rodan/playa/beaglebone/usermode/vs1063.c

#include <unistd.h>
#include <stdlib.h>
#include <string.h>
#include <sys/stat.h>
#include <fcntl.h>
#include <stdio.h>

#include "config.h"
#include "vs1063.h"
#include "event_gpio.h"
#include "spi.h"

//#include "patches/vs1063a-encpatches.plg"
//#include "patches/vs1063a-encpatchesflac.plg"
//#include "patches/vs1063a-patches-latm.plg"
//#include "patches/vs1063a-patches.plg"
//#include "patches/vs1063a-playflaccrc.plg"
#include "patches/vs1063a-playpatches.plg"

// How many transferred bytes between collecting data.
// A value between 1-8 KiB is typically a good value.
// If REPORT_ON_SCREEN is defined, a report is given on screen each time
// data is collected.
#define REPORT_INTERVAL 8192

uint8_t vs_vol_r, vs_vol_l;
int spidev_fd_xCS, spidev_fd_xDCS;
struct spi_ioc_transfer tr_xCS, tr_xDCS;

uint32_t vs_sm_state;
uint32_t vs_sm_target;
vs_stream_t vs_stream;

//int fd_debug;

void vs_set_state(const uint32_t state)
{
    vs_sm_state = state;
}

void vs_set_target(const uint32_t state)
{
    vs_sm_target = state;
}

void vs_assert_xreset()
{
    gpio_set_value(RST_GPIO, 0);
}

void vs_deassert_xreset()
{
    gpio_set_value(RST_GPIO, 1);
}

uint32_t vs_get_dreq()
{
    uint32_t ret;
    gpio_get_value(DREQ_GPIO, &ret);
    return ret;
}

// read the 16-bit value of a VS10xx register
uint16_t vs_read_register(const uint8_t address, const uint8_t flags)
{
    uint16_t rv = 0;
    uint8_t tx[4] = { VS_READ_COMMAND, address, 0xff, 0xff };
    uint8_t rx[4] = { 0, 0, 0, 0 };

    if (flags == WAIT_FOR_DREQ) {
        vs_wait(VS_DREQ_TMOUT);
    }
    spi_transfer(rx, tx, 4, spidev_fd_xCS, &tr_xCS);
    rv = rx[2] << 8 | rx[3];
    if (flags == WAIT_FOR_DREQ) {
        vs_wait(VS_DREQ_TMOUT);
    }
    return rv;
}

// write VS10xx register
void vs_write_register_hl(const uint8_t address, const uint8_t highbyte, const uint8_t lowbyte,
                          const uint8_t flags)
{
    uint8_t tx[4] = { VS_WRITE_COMMAND, address, highbyte, lowbyte };
    uint8_t rx[4] = { 0, 0, 0, 0 };
    if (flags == WAIT_FOR_DREQ) {
        vs_wait(VS_DREQ_TMOUT);
    }
    spi_transfer(rx, tx, 4, spidev_fd_xCS, &tr_xCS);
    if (flags == WAIT_FOR_DREQ) {
        vs_wait(VS_DREQ_TMOUT);
    }
}

// write VS10xx 16-bit SCI registers
void vs_write_register(const uint8_t address, const uint16_t value, const uint8_t flags)
{
    uint8_t highbyte;
    uint8_t lowbyte;

    highbyte = (value & 0xff00) >> 8;
    lowbyte = value & 0x00ff;
    vs_write_register_hl(address, highbyte, lowbyte, flags);
}

// read data rams
uint16_t vs_read_wramaddr(const uint16_t address)
{
    uint16_t rv = 0;
    vs_write_register(SCI_WRAMADDR, address, WAIT_FOR_DREQ);
    rv = vs_read_register(SCI_WRAM, WAIT_FOR_DREQ);
    return rv;
}

// write to data rams
void vs_write_wramaddr(const uint16_t address, const uint16_t value)
{
    vs_write_register(SCI_WRAMADDR, address, WAIT_FOR_DREQ);
    vs_write_register(SCI_WRAM, value, WAIT_FOR_DREQ);
}

uint8_t vs_xfer_test(uint16_t value1, uint16_t value2)
{
    uint16_t ret_val1, ret_val2;

    vs_write_register(SCI_AICTRL1, value1, WAIT_FOR_DREQ);
    vs_write_register(SCI_AICTRL2, value2, WAIT_FOR_DREQ);

    ret_val1 = vs_read_register(SCI_AICTRL1, WAIT_FOR_DREQ);
    ret_val2 = vs_read_register(SCI_AICTRL2, WAIT_FOR_DREQ);

    if (ret_val1 != value1) {
        printf("%d != %d\n", ret_val1, value1);
        return EXIT_FAILURE;
    }
    if (ret_val2 != value2) {
        printf("%d != %d\n", ret_val2, value2);
        return EXIT_FAILURE;
    }

    vs_write_register(SCI_AICTRL1, 0, WAIT_FOR_DREQ);
    vs_write_register(SCI_AICTRL2, 0, WAIT_FOR_DREQ);

    ret_val1 = vs_read_register(SCI_AICTRL1, WAIT_FOR_DREQ);
    ret_val2 = vs_read_register(SCI_AICTRL2, WAIT_FOR_DREQ);

    if (ret_val1 != 0) {
        return EXIT_FAILURE;
    }
    if (ret_val2 != 0) {
        return EXIT_FAILURE;
    }

    return EXIT_SUCCESS;
}

// wait for VS_DREQ to get HIGH before sending new data to SPI
uint8_t vs_wait(uint16_t timeout)
{
    while (timeout--) {
        if (vs_get_dreq()) {
            return EXIT_SUCCESS;
        }
        usleep(15);
    }
    return EXIT_FAILURE;
}

// DREQ interrupt handler
static void vs1063_handler(unsigned int gpio)
{
    //event_detected(gpio);
    vs_state_machine();
}

void vs_close()
{
    // switch to blocking functions after the IRQ is disabled
    //vs_set_target(VS_SMT_STOP);
    //vs_set_state(VS_SM_IDLE);
    remove_edge_detect(DREQ_GPIO);
    usleep(1000);

    //vs_set_volume(0xfe, 0xfe);
    vs_end_play();

    close(spidev_fd_xCS);
    close(spidev_fd_xDCS);
    gpio_unexport(RST_GPIO);
    gpio_unexport(DREQ_GPIO);
}

void vs_soft_reset(void)
{
    vs_write_register(SCI_MODE, SM_SDINEW | SM_RESET, WAIT_FOR_DREQ);
    usleep(2000);
    vs_write_register(SCI_CLOCKF, 0xb000, WAIT_FOR_DREQ);
    usleep(200);
}

// setup I2S (see page77 of the datasheet of vs1053 )
// also enables blinky lights on the simple dsp evaluation board
void vs_setup_i2s(void)
{
    //set GPIO0 as output
    vs_write_wramaddr(0xc017, 0x00f0);
    //enable I2S (MCLK enabled, 48kHz sample rate)
    vs_write_wramaddr(0xc040, 0x000c);  // I2S_CF_MCLK_ENA | I2S_CF_ENA
}

// set VS10xx volume attenuation    0x00 lound - 0xfe silent
void vs_set_volume(const uint8_t leftchannel, const uint8_t rightchannel)
{
    // volume = dB/0.5
    vs_write_register_hl(SCI_VOL, leftchannel, rightchannel, WAIT_FOR_DREQ);
}

// returns 0 on success
// returns the old codec id on failure
uint16_t vs_end_play(void)
{
    uint8_t i = 0;
    uint16_t rv;

    if ((vs_stream.fd != -1) && (vs_sm_state == VS_REPLENISH_BUF)) {
        close(vs_stream.fd);
        vs_stream.fd = -1;
        vs_write_register(SCI_MODE, SM_CANCEL, WAIT_FOR_DREQ);
        if (vs_stream.fill_cnt) {
            vs_fill(vs_stream.fill_byte, vs_stream.fill_cnt);
        }

        vs_write_register(SCI_MODE, SM_CANCEL, WAIT_FOR_DREQ);
        vs_fill(vs_stream.fill_byte, 32);
        while (vs_read_register(SCI_MODE, WAIT_FOR_DREQ) & SM_CANCEL) {
            vs_fill(vs_stream.fill_byte, 32);
            i++;
            if (i == 64) {
                vs_soft_reset();
                break;
            }
        }
        vs_sm_state = VS_SM_IDLE;
    }
    rv = vs_read_register(SCI_HDAT1, WAIT_FOR_DREQ);
    return rv;
}

void vs_fill(const uint8_t fill_byte, const uint16_t len)
{
    uint8_t buf[VS_BUFF_SZ];
    uint16_t i = 0;

    memset(buf, fill_byte, VS_BUFF_SZ);

    for (i = 0; i < (len / VS_BUFF_SZ); i++) {
        vs_wait(VS_DREQ_TMOUT);
        spi_transfer(NULL, buf, VS_BUFF_SZ, spidev_fd_xDCS, &tr_xDCS);
    }
    if (len % VS_BUFF_SZ) {
        vs_wait(VS_DREQ_TMOUT);
        spi_transfer(NULL, buf, len % VS_BUFF_SZ, spidev_fd_xDCS, &tr_xDCS);
    }
}

// level    0 - disabled - suited for listening through loudspeakers
//          1 - suited for listening to normal musical scores with headphones
//          2 - less subtle than 1
//          3 - for old and 'dry' recordings
void vs_ear_speaker(const uint8_t level)
{
    const uint16_t ear_speaker_level[4] = { 0, 0x2ee0, 0x9470, 0xc350 };

    vs_write_wramaddr(earSpeakerLevel, ear_speaker_level[level % 4]);
}

uint16_t vs_get_fill_cnt(const uint16_t file_type)
{
    if (file_type == 0x7665) {
        //printf("riff\n");
        return SDI_END_FILL_BYTES;
    } else if (file_type == 0x4154) {
        //printf("aacAdts\n");
        return SDI_END_FILL_BYTES;
    } else if (file_type == 0x4144) {
        //printf("aacAdif\n");
        return SDI_END_FILL_BYTES;
    } else if (file_type == 0x574d) {
        //printf("wma\n");
        return SDI_END_FILL_BYTES;
    } else if (file_type == 0x4f67) {
        //printf("OggVorbis\n");
        return SDI_END_FILL_BYTES;
    } else if (file_type == 0x664c) {
        //printf("flac\n");
        return SDI_END_FILL_BYTES_FLAC;
    } else if (file_type == 0x4d34) {
        //printf("aacMp4\n");
        return SDI_END_FILL_BYTES;
    } else if ((file_type & 0xffe6) == 0xffe2) {
        //printf("mp3\n");
        return SDI_END_FILL_BYTES;
    } else if ((file_type & 0xffe6) == 0xffe4) {
        //printf("mp2\n");
        return SDI_END_FILL_BYTES;
    } else if ((file_type & 0xffe6) == 0xffe6) {
        //printf("mp1\n");
        return SDI_END_FILL_BYTES;
    } else {
        //printf("unknown\n");
        return SDI_END_FILL_BYTES_FLAC;
    }

    return SDI_END_FILL_BYTES_FLAC;
}

uint16_t vs_end_play_irq(void)
{
    vs_set_target(VS_SMT_STOP);
    vs_set_state(VS_SM_MODE_CANCEL);
    return EXIT_SUCCESS;
}

uint8_t vs_play_file(const char *file_path)
{
    if ((vs_stream.fd = open(file_path, O_RDONLY)) == -1) {
        return EXIT_FAILURE;
    }
    memset(vs_stream.buf, 0, BUFF_SIZE);
    vs_stream.buf_remain = 0;
    vs_stream.file_type = 0;
    vs_stream.fill_stage = 0;
    vs_stream.fill_byte = 0;
    vs_stream.data_ctr = 0;
    vs_stream.data_rep = REPORT_INTERVAL;
    vs_set_target(VS_SMT_PLAY);
    vs_set_state(VS_RST_DECODE_TIME);
    vs_state_machine();

    return EXIT_SUCCESS;
}

void vs_load_patch(void)
{
    int i = 0;

    while (i < sizeof(plugin) / sizeof(plugin[0])) {
        unsigned short addr, n, val;
        addr = plugin[i++];
        n = plugin[i++];
        if (n & 0x8000U) {      // RLE run, replicate n samples
            n &= 0x7FFF;
            val = plugin[i++];
            while (n--) {
                vs_write_register(addr, val, WAIT_FOR_DREQ);
            }
        } else {                // Copy run, copy n samples
            while (n--) {
                val = plugin[i++];
                vs_write_register(addr, val, WAIT_FOR_DREQ);
            }
        }
    }
}

int vs_init(void)
{
    BBIO_err rl;

    if ((spidev_fd_xCS = spi_init("/dev/spidev2.1", &tr_xCS)) == -1) {
        return VS_ERR_SPI_INIT;
    }
    if ((spidev_fd_xDCS = spi_init("/dev/spidev2.0", &tr_xDCS)) == -1) {
        return VS_ERR_SPI_INIT;
    }
    // VLSI RST signal pin
    rl = gpio_export(RST_GPIO);
    if (rl != BBIO_OK) {
        return VS_ERR_GPIO_ATTACH;
    }

    rl = gpio_set_direction(RST_GPIO, OUTPUT);
    if (rl != BBIO_OK) {
        return VS_ERR_GPIO_ATTACH;
    }
    // VLSI DREQ signal pin
    rl = add_edge_detect(DREQ_GPIO, RISING_EDGE);
    if (rl > 0) {
        return VS_ERR_GPIO_ATTACH;
    }
    // initial port states
    vs_assert_xreset();
    usleep(2000);
    vs_deassert_xreset();
    sleep(1);

    // software reset, chip init
    vs_write_register(SCI_MODE, SM_SDINEW | SM_RESET | SM_TESTS, WAIT_FOR_DREQ);

    // test SPI read/write
    if (vs_xfer_test(0xe1ac, 0x479b) != EXIT_SUCCESS) {
        return VS_ERR_SPI_XFER;
    }
    // check vlsi chip version
    if (((vs_read_register(SCI_STATUS, WAIT_FOR_DREQ) >> 4) & 15) != 6) {
        return VS_ERR_WRONG_VS_VER;
    }
    // disable audio output
    vs_write_register_hl(SCI_VOL, 0xff, 0xff, WAIT_FOR_DREQ);

    // set vs clock
    vs_write_register(SCI_CLOCKF, 0xb000, WAIT_FOR_DREQ);

    // increase SPI speeds
    spi_set_speed(spidev_fd_xCS, &tr_xCS, 2000000);
    spi_set_speed(spidev_fd_xDCS, &tr_xDCS, 2000000);

    // test SPI read/write
    if (vs_xfer_test(0xabad, 0x7e57) != EXIT_SUCCESS) {
        return VS_ERR_SPI_XFER;
    }
    // Declick: Slow sample rate for slow analog part startup
    vs_write_register_hl(SCI_AUDATA, 0, 10, WAIT_FOR_DREQ);       // 10Hz
    // Switch on the analog parts
    vs_write_register_hl(SCI_AUDATA, 0xac, 0x45, WAIT_FOR_DREQ);  // 44100Hz, stereo

    // AVDD is at least 3.3v, so select 1.65v reference to increase
    // the analog output swing
    vs_write_register(SCI_STATUS, SS_REFERENCE_SEL, WAIT_FOR_DREQ);

	// check http://www.vlsi.fi/en/support/software/vs10xxpatches.html
    vs_load_patch();

    // set the default volume
    vs_write_register_hl(SCI_VOL, vs_vol_l, vs_vol_r, WAIT_FOR_DREQ);

    // from this point onwards all SCI/SDI commands must be NO_WAIT_FOR_DREQ
    // and sent via vs_state_machine()
    rl = add_edge_callback(DREQ_GPIO, vs1063_handler);
    if (rl != 0) {
        return VS_ERR_GPIO_ATTACH;
    }
    vs_vol_r = VS_DEFAULT_VOL;
    vs_vol_l = VS_DEFAULT_VOL;

    return EXIT_SUCCESS;
}

void vs_state_machine()
{
    uint16_t tx_len;

 again:
    switch (vs_sm_state) {
    case VS_SM_IDLE:
        printf("VS_SM_IDLE\n");
        break;
    case VS_RST_DECODE_TIME:
        vs_write_register(SCI_DECODE_TIME, 0, NO_WAIT_FOR_DREQ);
        vs_sm_state = VS_REPLENISH_BUF;
        break;
    case VS_REPLENISH_BUF:
        if (vs_stream.fd < 1) {
            vs_sm_state = VS_SM_IDLE;
            goto again;
        }
        if (vs_stream.buf_remain == 0) {
            printf("\nreplenish buf from %d\n", vs_stream.fd);
            memset(vs_stream.buf, 0, BUFF_SIZE);
            vs_stream.read_len = read(vs_stream.fd, vs_stream.buf, BUFF_SIZE);
            if (vs_stream.read_len == 0) {
                printf("stream has ended\n");
                close(vs_stream.fd);
                vs_stream.fd = -1;
                vs_sm_state = VS_SM_MODE_CANCEL;
                goto again;
                break;
            }
            vs_stream.buf_remain = vs_stream.read_len;
        }
        // DREQ is unafected at this point
        // fallthrough
    case VS_SEND_STREAM:
        // stop sending if internal buffer is empty or if #DREQ has been asserted
        //printf("%d remain ", vs_stream.buf_remain);
        while (vs_get_dreq()) {
            if (vs_stream.buf_remain < VS_BUFF_SZ) {
                tx_len = vs_stream.buf_remain;
            } else {
                tx_len = VS_BUFF_SZ;
            }

            if (tx_len > 0) {
                tr_xDCS.rx_buf = 0;
                tr_xDCS.tx_buf =
                    (unsigned long)vs_stream.buf + (vs_stream.read_len - vs_stream.buf_remain);
                tr_xDCS.len = tx_len;
                spi_transfer_sp(spidev_fd_xDCS, &tr_xDCS);
                vs_stream.buf_remain -= tx_len;
                vs_stream.data_ctr += tx_len;
            }

            if (vs_stream.buf_remain == 0) {
                // get more data
                memset(vs_stream.buf, vs_stream.fill_byte, BUFF_SIZE);
                vs_stream.read_len = read(vs_stream.fd, vs_stream.buf, BUFF_SIZE);
                if (vs_stream.read_len == 0) {
                    printf("stream has ended\n");
                    close(vs_stream.fd);
                    vs_stream.fd = -1;
                    vs_sm_state = VS_SM_MODE_CANCEL;
                    goto again;
                    break;
                }
                vs_stream.buf_remain = vs_stream.read_len;
            }
        }
        // DREQ is now low, do some maintenance
        // refresh stream play status report if needed
        if (vs_stream.data_ctr > vs_stream.data_rep) {
            vs_stream.fill_cnt = vs_get_fill_cnt(vs_stream.file_type);
            //printf("0x%x, 0x%x, %u\n", vs_stream.file_type, vs_stream.fill_byte,
            //       vs_stream.fill_cnt);
            vs_stream.data_rep = vs_stream.data_ctr + REPORT_INTERVAL;

            // detect if the vs_sm_state has been modified from the main thread
            if (vs_sm_state != VS_REPLENISH_BUF) {
                goto again;
                break;
            }

            if (!vs_stream.file_type) {
                vs_sm_state = VS_SM_READ_HDAT1;
                goto again;
                break;
            }

            vs_sm_state = VS_SM_GET_FILL_BYTE;
            goto again;
            break;
        }

        break;
    case VS_SM_GET_REPORT:
        // fallthrough
    case VS_SM_READ_HDAT1:
        //printf("VS_SM_READ_HDAT1 at %d\n", vs_stream.data_ctr);
        if (vs_stream.fill_byte) {
            // we already got the fill_byte
            vs_sm_state = VS_REPLENISH_BUF;
            goto again;
            break;
        } else {
            vs_sm_state = VS_SM_GET_FILL_BYTE;
        }
        vs_stream.file_type = vs_read_register(SCI_HDAT1, NO_WAIT_FOR_DREQ);
        break;
    case VS_SM_GET_FILL_BYTE:
        // ignore the most-probably low DREQ and send the SCI commands
        vs_sm_state = VS_REPLENISH_BUF;
        vs_write_register(SCI_WRAMADDR, PAR_END_FILL_BYTE, NO_WAIT_FOR_DREQ);
        vs_stream.fill_byte = vs_read_register(SCI_WRAM, NO_WAIT_FOR_DREQ);
        break;
    case VS_SM_MODE_CANCEL:
        printf("VS_SM_MODE_CANCEL\n");
        vs_sm_state = VS_SM_CHECK_CANCEL;
        memset(vs_stream.buf, vs_stream.fill_byte, BUFF_SIZE);
        vs_write_register(SCI_MODE, SM_SDINEW | SM_CANCEL, NO_WAIT_FOR_DREQ);
        break;
    case VS_SM_CHECK_CANCEL:
        printf("VS_SM_CHECK_CANCEL\n");
        vs_sm_state = VS_SM_FILL_MNGR;
        vs_stream.reg = vs_read_register(SCI_MODE, NO_WAIT_FOR_DREQ);
        break;
    case VS_SM_FILL_MNGR:
        printf("VS_SM_FILL_MNGR\n");
        printf("SCI_MODE 0x%x\n", vs_stream.reg);
        if ((vs_stream.reg & SM_CANCEL) == 0) {
            if (vs_stream.fd != -1) {
                close(vs_stream.fd);
                vs_stream.fd = -1;
            }
            vs_sm_state = VS_SM_IDLE;
            goto again;
            break;
        } else {
            if (vs_stream.fill_stage == 0) {
                vs_stream.buf_remain = vs_stream.fill_cnt;
                vs_stream.fill_stage = 0;
                if (vs_stream.fd != -1) {
                    close(vs_stream.fd);
                    vs_stream.fd = -1;
                }
                vs_sm_state = VS_SM_FILL;
                goto again;
                break;
            }                   // FIXME add stage1,2 of fill
        }
        break;
    case VS_SM_FILL:
        printf("VS_SM_FILL %d\n", vs_stream.fill_stage);
        while (vs_get_dreq()) {
            if (vs_stream.buf_remain < VS_BUFF_SZ) {
                tx_len = vs_stream.buf_remain;
            } else {
                tx_len = VS_BUFF_SZ;
            }

            if (tx_len > 0) {
                tr_xDCS.rx_buf = 0;
                tr_xDCS.tx_buf = (unsigned long)vs_stream.buf;  // we only send the first <=VS_BUFF_SZ bytes
                tr_xDCS.len = tx_len;
                spi_transfer_sp(spidev_fd_xDCS, &tr_xDCS);
                vs_stream.buf_remain -= tx_len;
            }

            if (vs_stream.buf_remain == 0) {
                vs_stream.fill_stage++;
                vs_sm_state = VS_SM_MODE_CANCEL;
                goto again;
                break;
            }
        }
        break;
    }
}
