rodan/playa/beaglebone/usermode/config.h

#ifndef _CONFIG_H_
#define _CONFIG_H_

//#define CONFIG_DEBUG

// RST is on P9_27,GPIO3_19,3*32+19
#define     RST_GPIO  115
#define      RST_KEY  "P9_27"

// DREQ is on P9_25,GPIO3_21,3*32+21
#define    DREQ_GPIO  117
#define     DREQ_KEY  "P9_25"

#endif
